lucasdmr24/Funbio-Proyecto/Documentacion/Entregables/Entregable 2/Entregable 2 Corregido.md

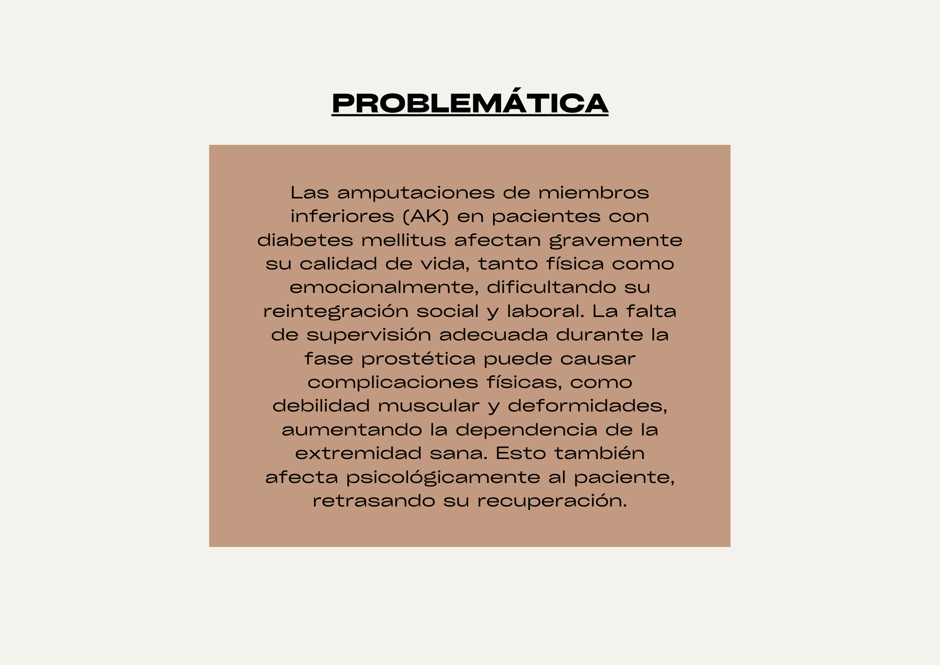
[picture p74: Documentacion/Entregables/Entregable 2/image_0.png]
image alt text
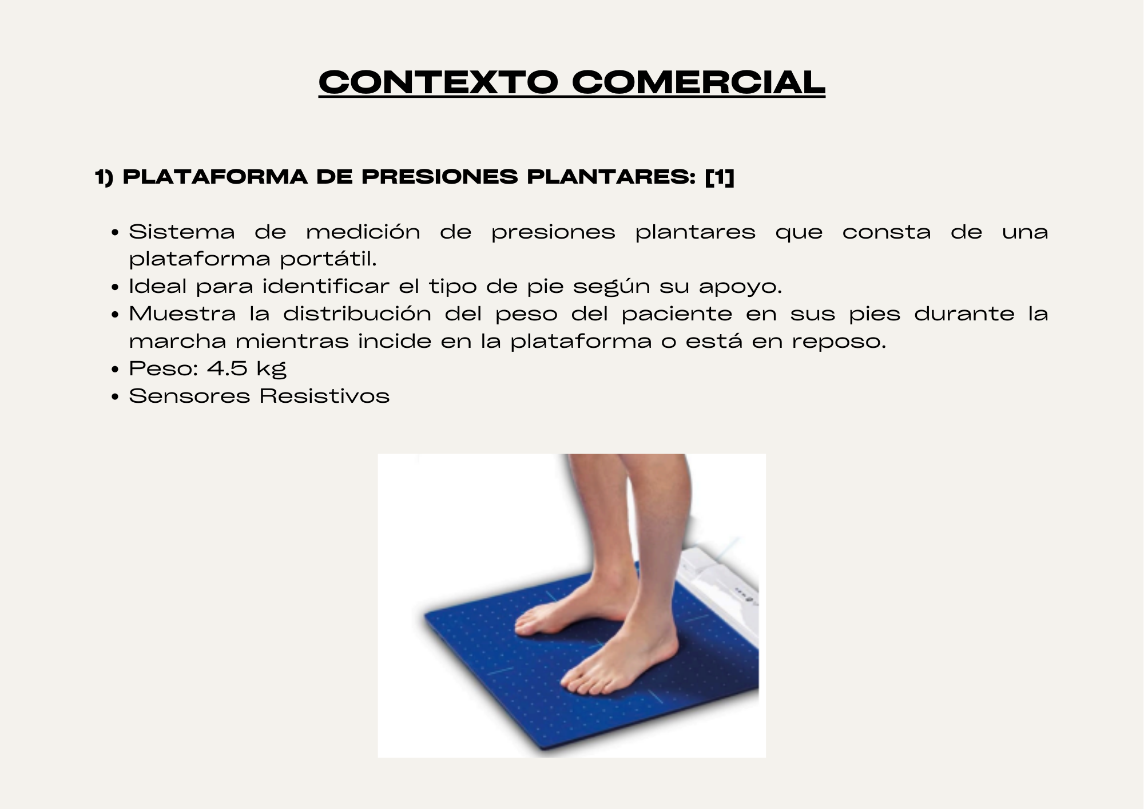
[picture p75: Documentacion/Entregables/Entregable 2/image_1.png]
image alt text
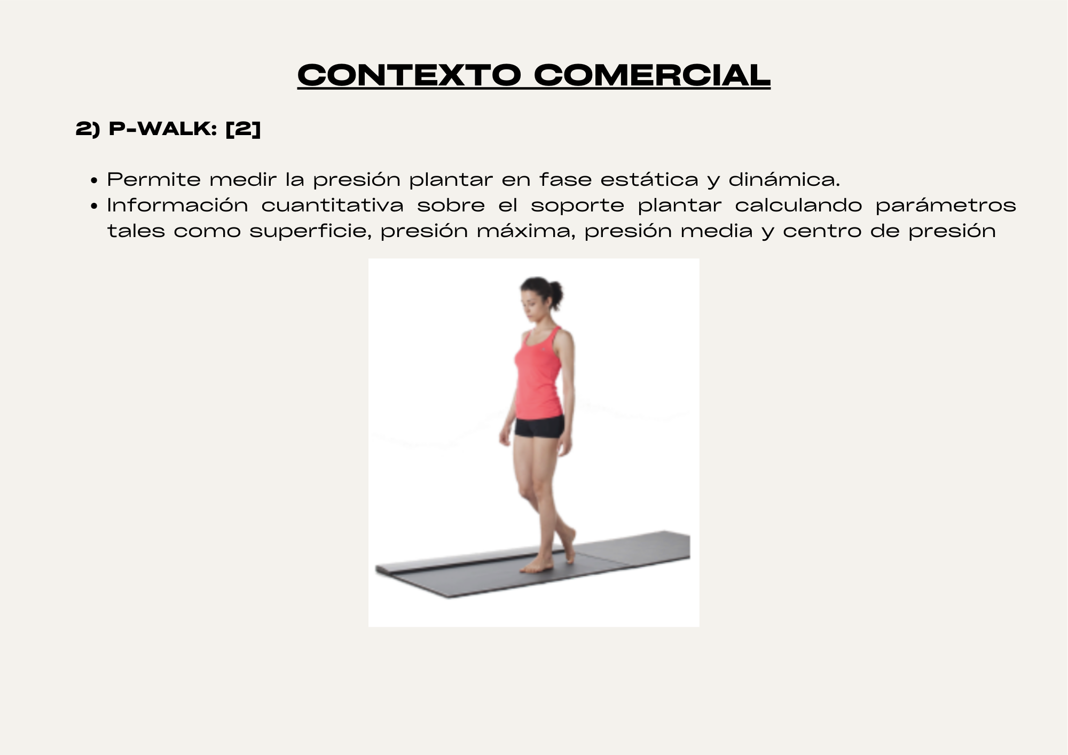
[picture p76: Documentacion/Entregables/Entregable 2/image_2.png]
image alt text
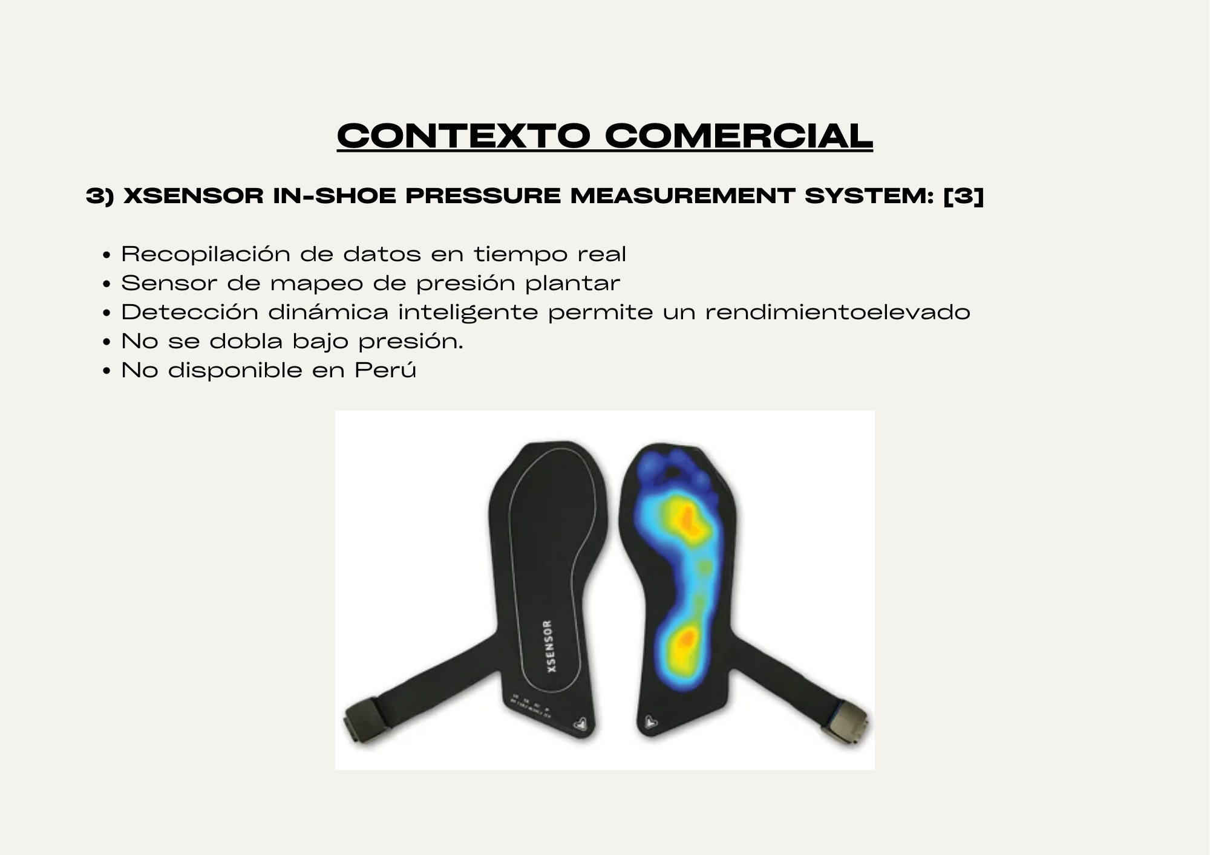
[picture p77: Documentacion/Entregables/Entregable 2/image_3.png]
image alt text
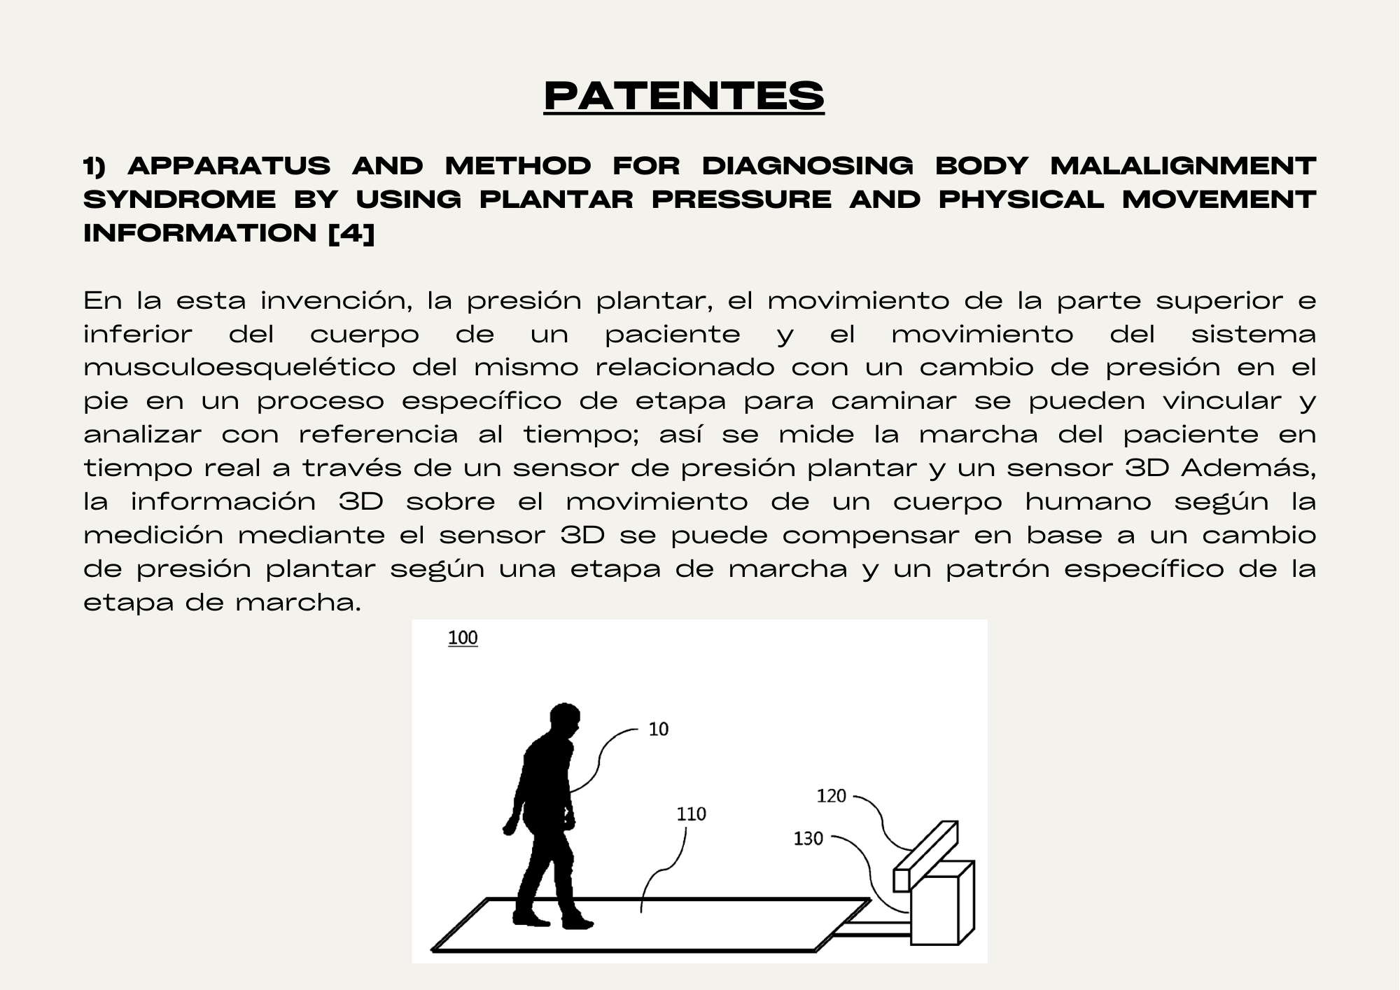
[picture p78: Documentacion/Entregables/Entregable 2/image_4.png]
image alt text
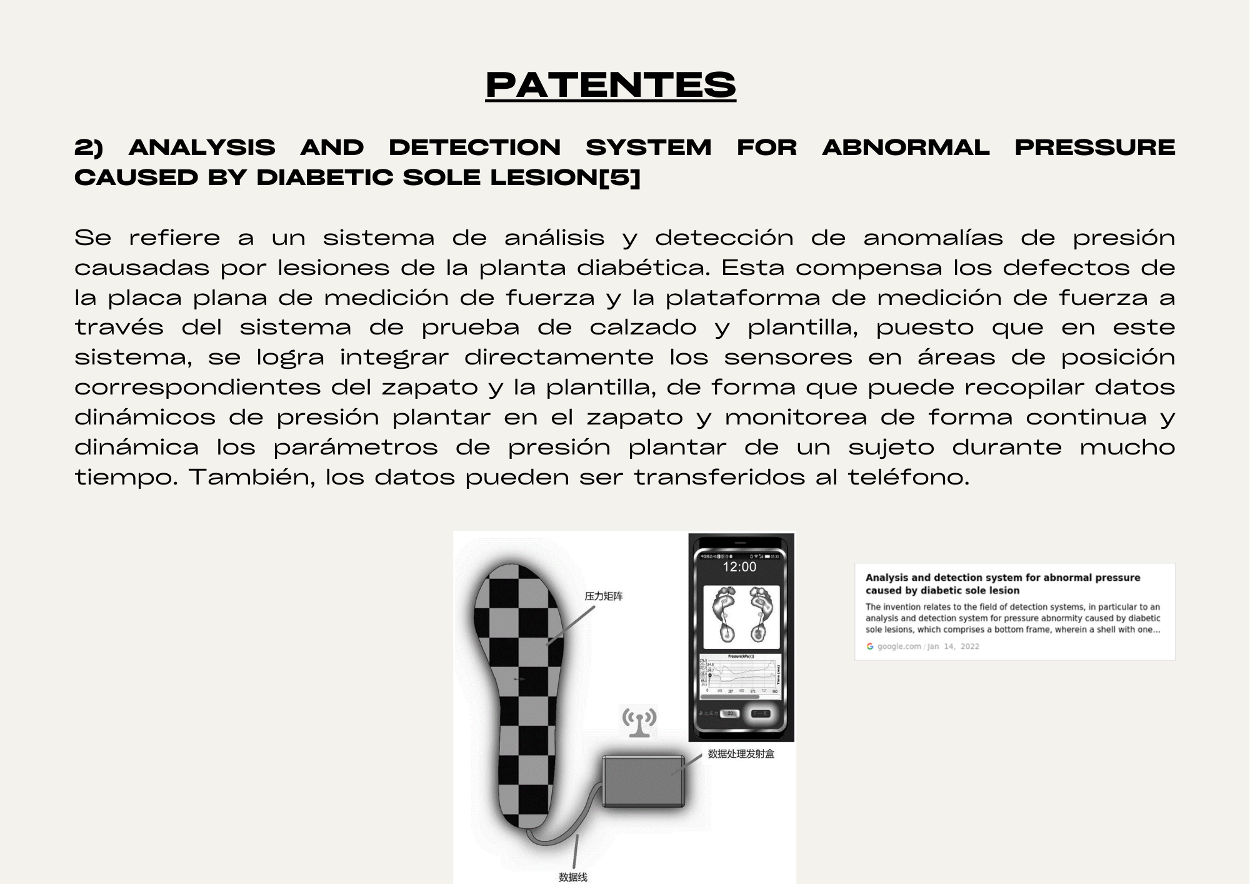
[picture p79: Documentacion/Entregables/Entregable 2/image_5.png]
image alt text
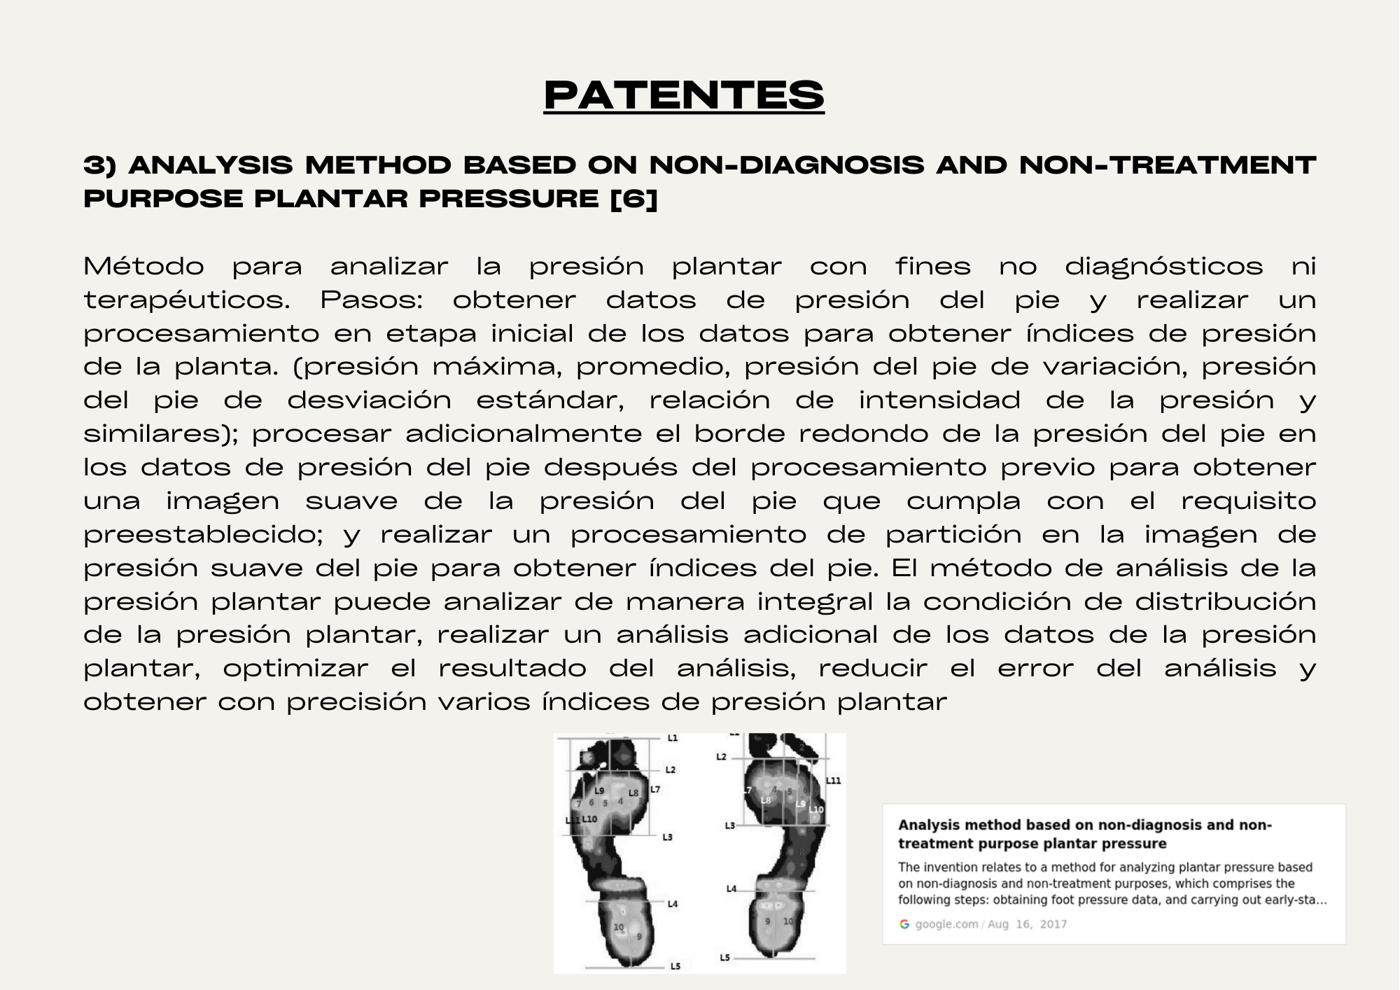
[picture p80: Documentacion/Entregables/Entregable 2/image_6.png]
image alt text
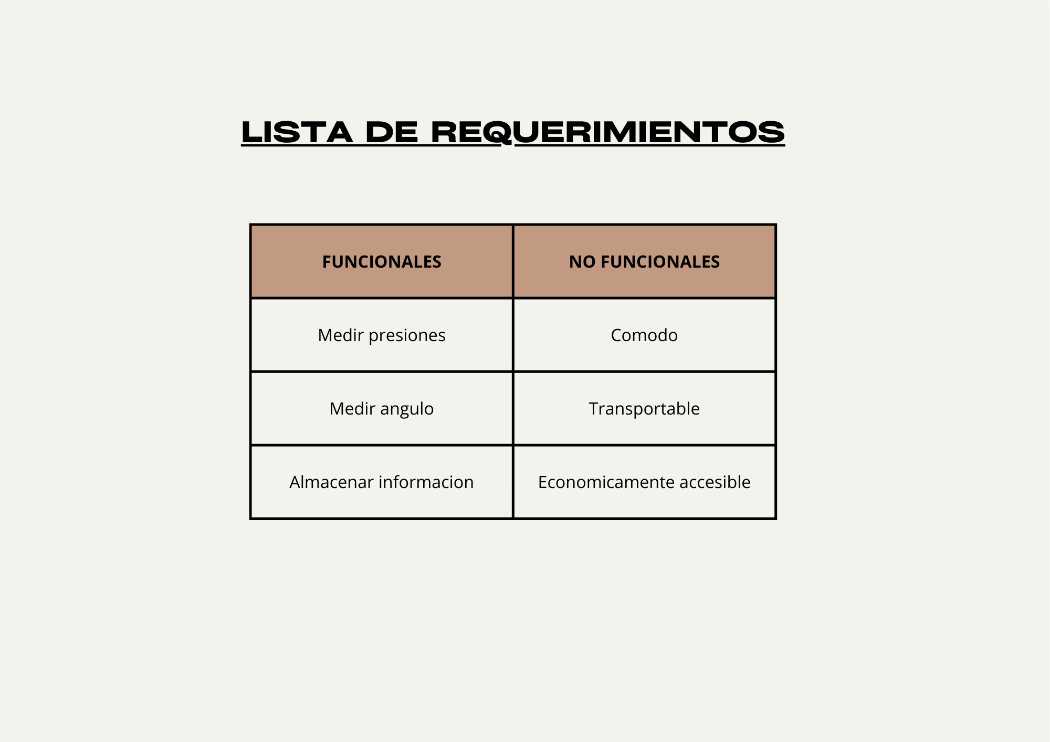
[picture p81: Documentacion/Entregables/Entregable 2/image_7.png]
image alt text
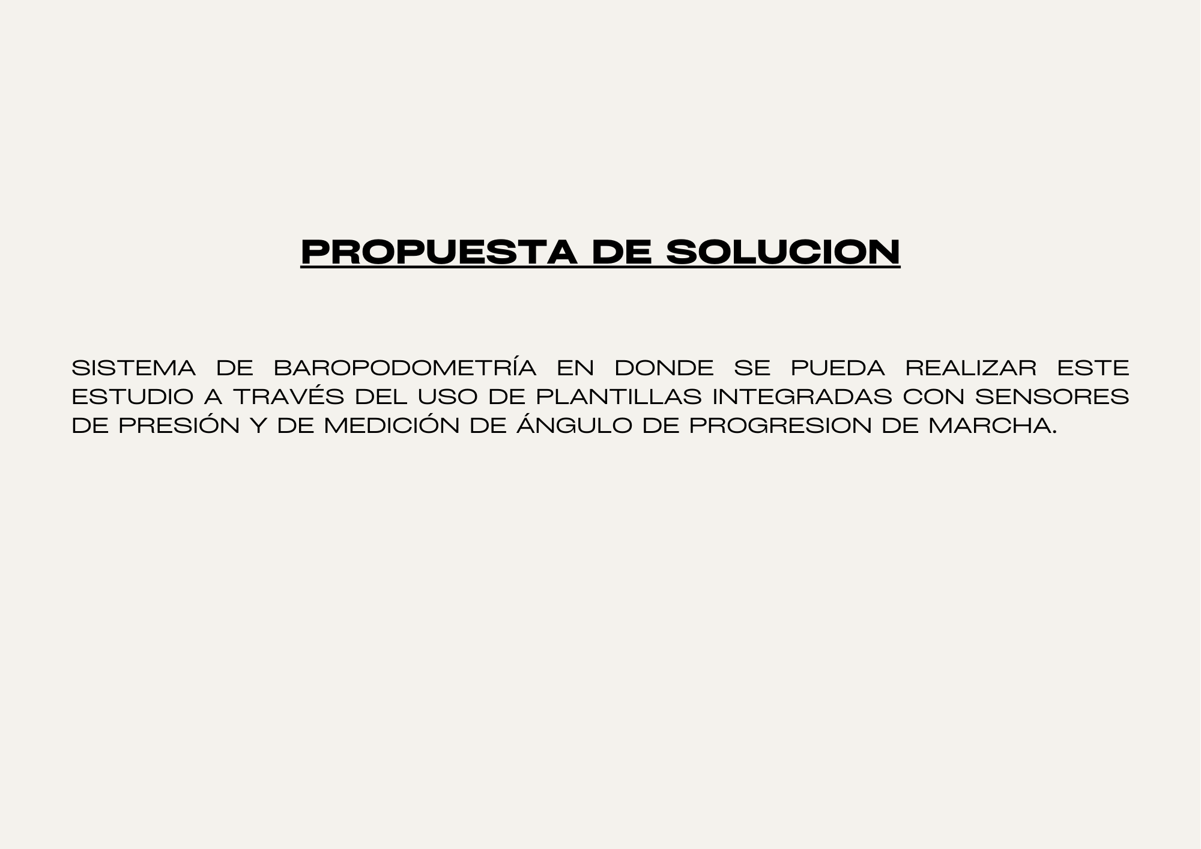
[picture p82: Documentacion/Entregables/Entregable 2/image_8.png]
image alt text
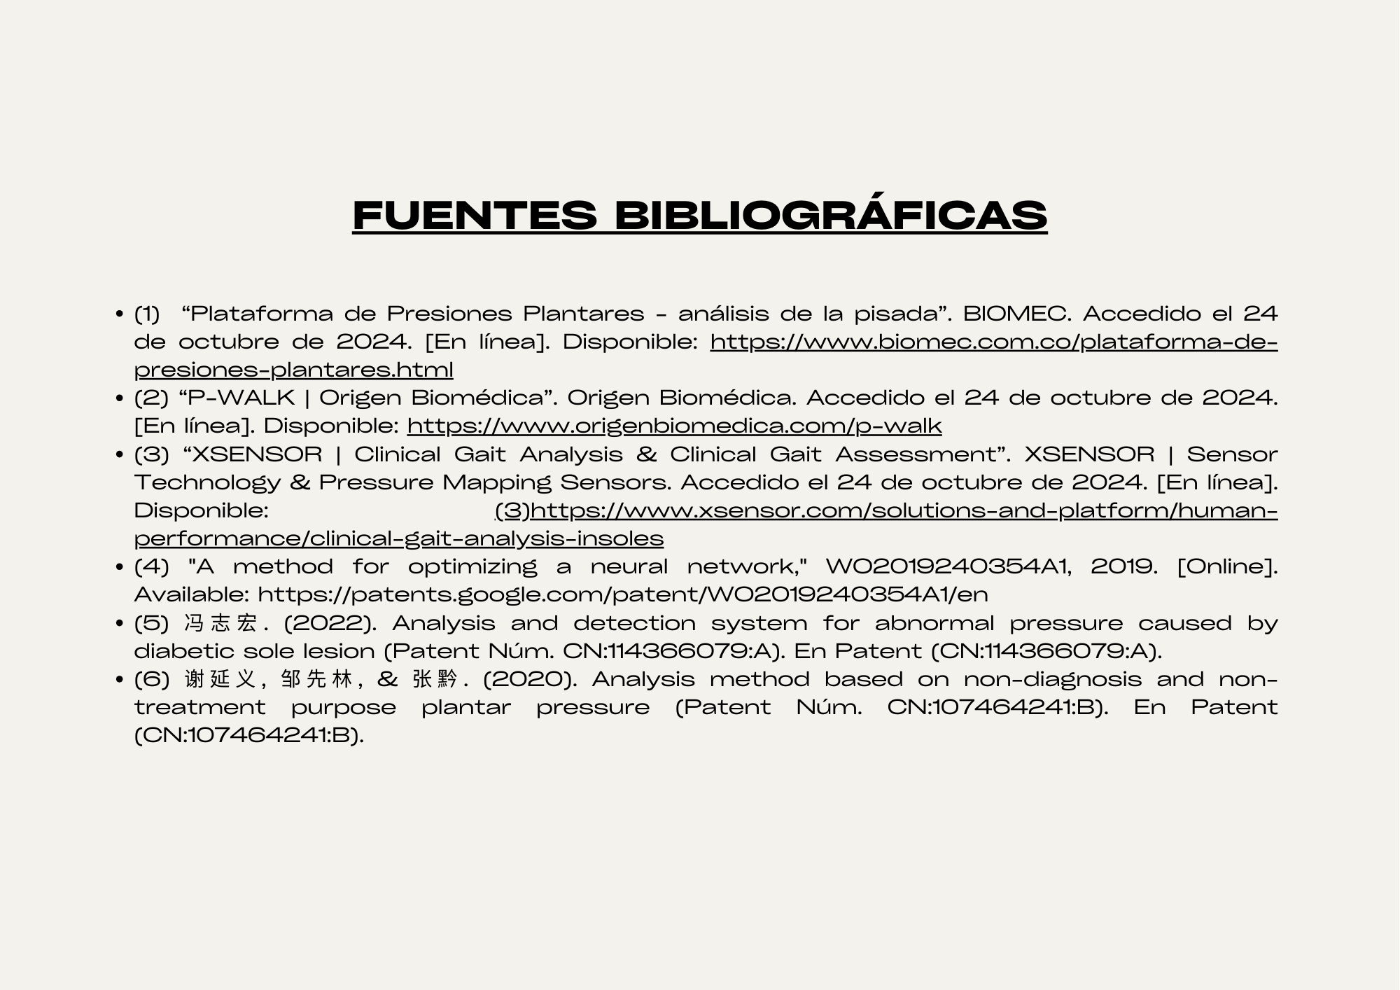
[picture p83: Documentacion/Entregables/Entregable 2/image_9.png]
image alt text
