lucasdmr24/Funbio-Proyecto/Imagenes/Entregable 1/image_0.png

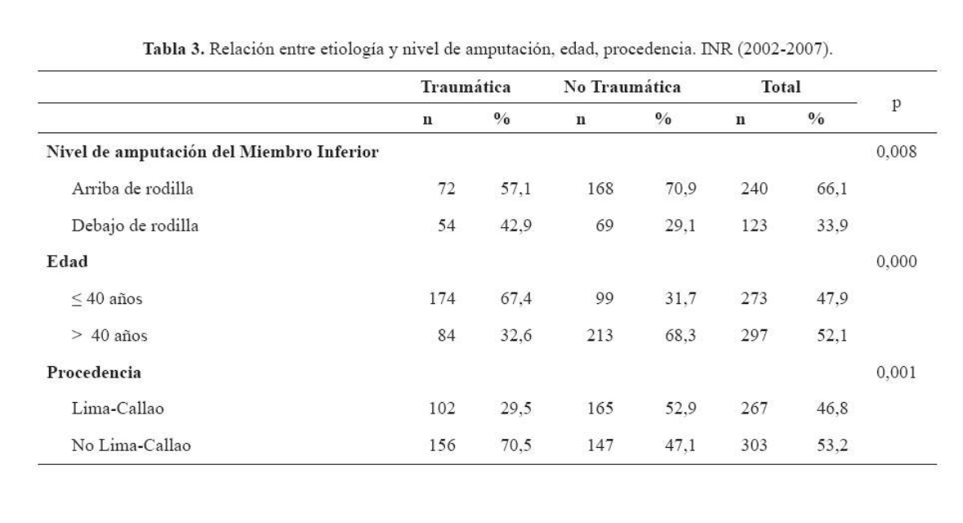
Imagenes/Entregable 1/image_0.png
