lucasdmr24/Funbio-Proyecto/Imagenes/Entregable 1/image_1.jpg

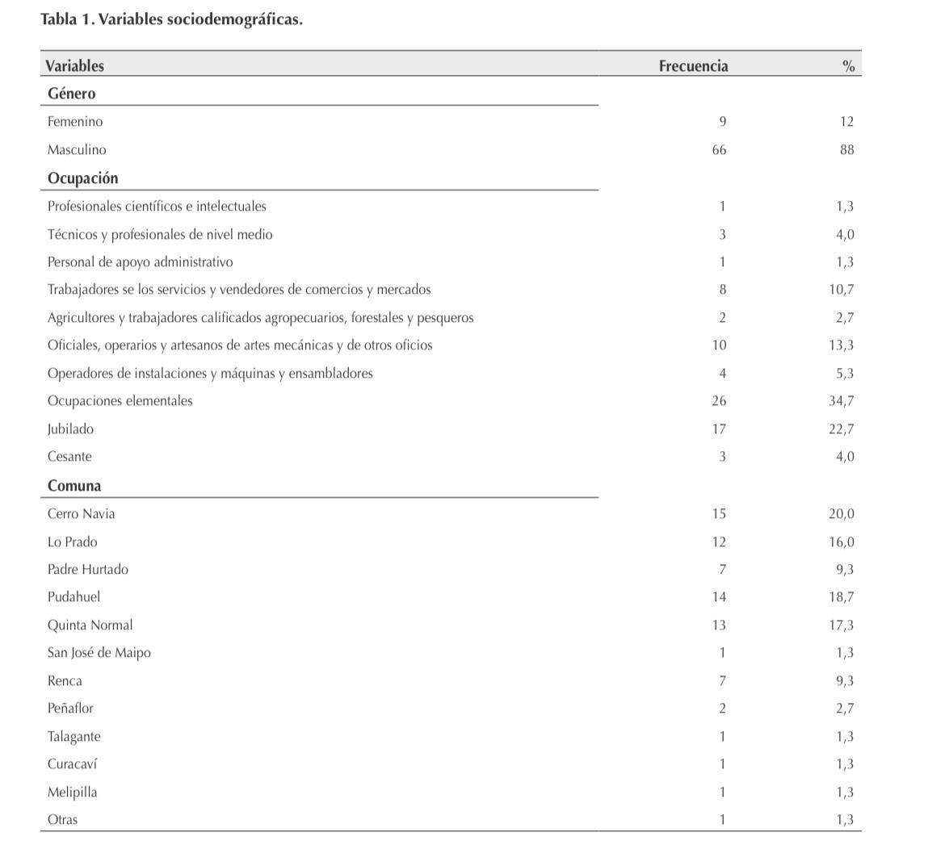
Imagenes/Entregable 1/image_1.jpg
