lucasdmr24/Funbio-Proyecto/Imagenes/Entregable 1/image_2.jpg

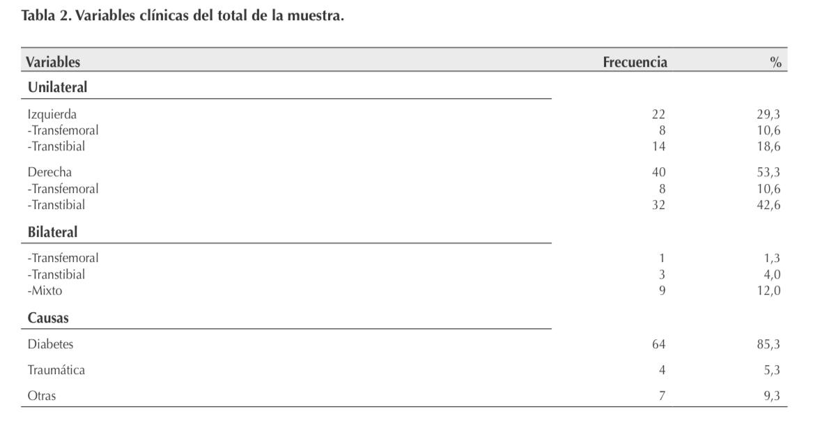
Imagenes/Entregable 1/image_2.jpg
