lucasdmr24/Funbio-Proyecto/Imagenes/Entregable 1/image_3.jpg

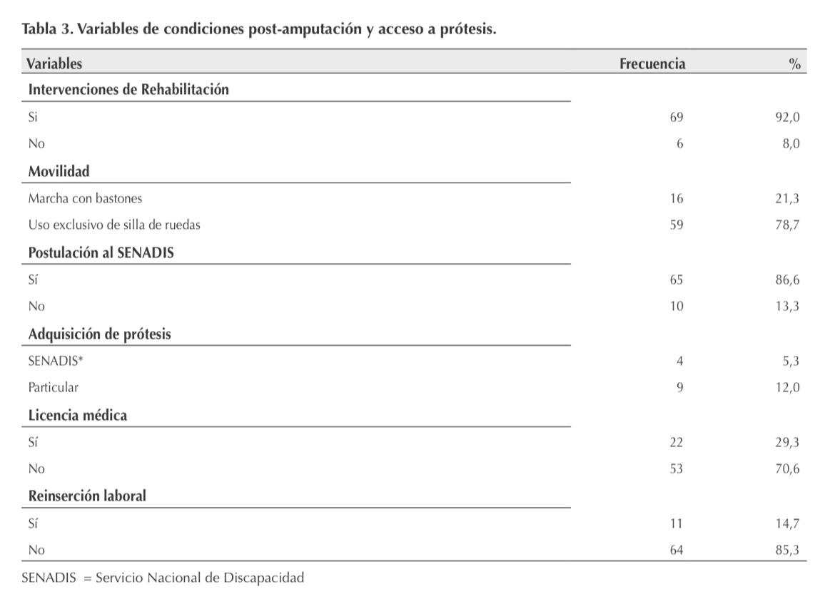
Imagenes/Entregable 1/image_3.jpg
