lucasdmr24/Funbio-Proyecto/Imagenes/Entregable 1/image_4.jpg

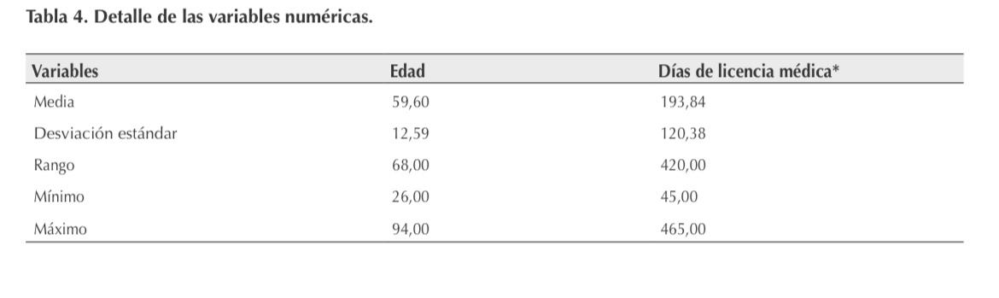
Imagenes/Entregable 1/image_4.jpg
