lucasdmr24/Funbio-Proyecto/Imagenes/Entregable 1/image_5.jpg

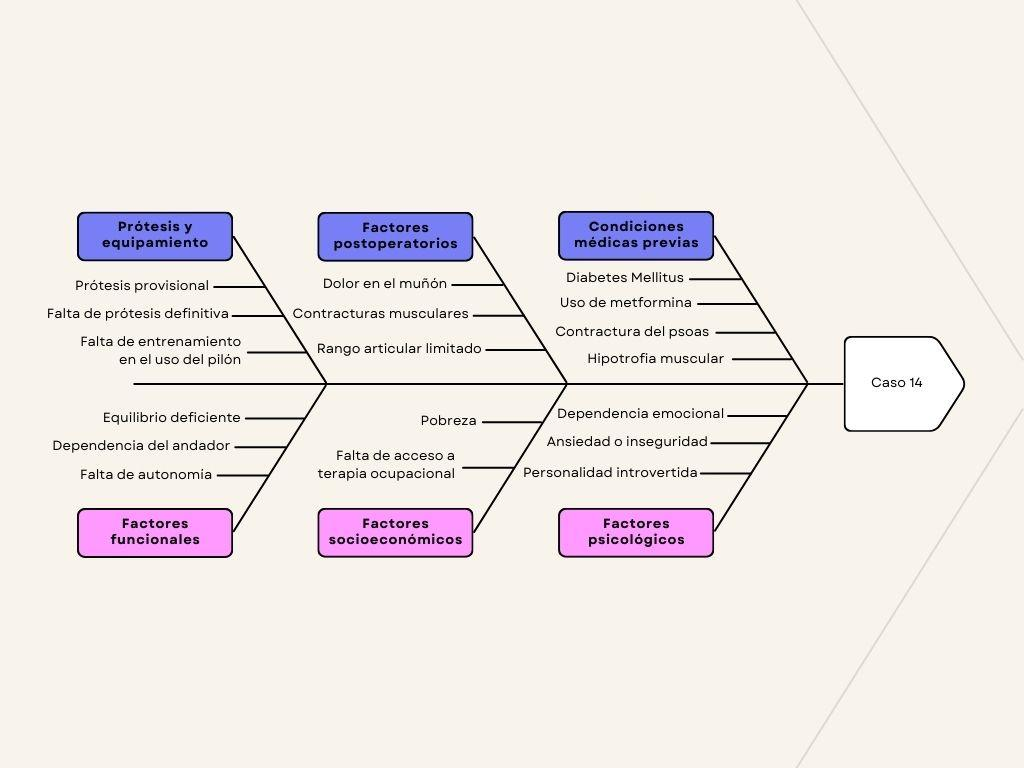
Imagenes/Entregable 1/image_5.jpg
