lucasdmr24/Funbio-Proyecto/Imagenes/Entregable 1/image_6.png

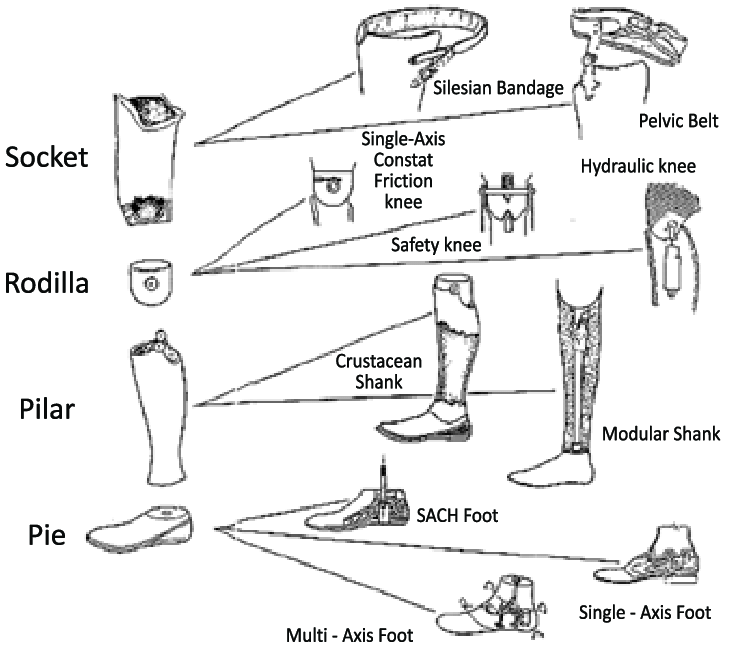
Imagenes/Entregable 1/image_6.png
