lucasdmr24/Funbio-Proyecto/Imagenes/Entregable 1/image_7.png

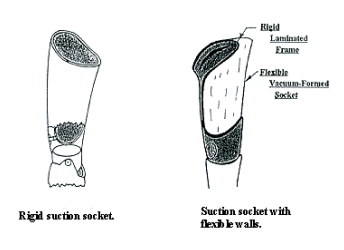
Imagenes/Entregable 1/image_7.png
