lucasdmr24/Funbio-Proyecto/Imagenes/Entregable 1/image_8.png

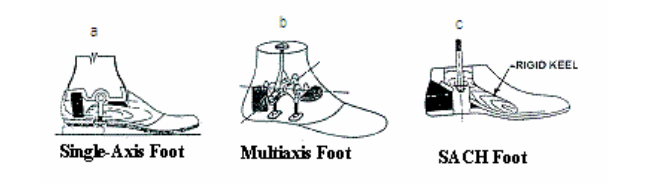
Imagenes/Entregable 1/image_8.png
