lucasdmr24/Funbio-Proyecto/Imagenes/Entregable 1/image_9.png

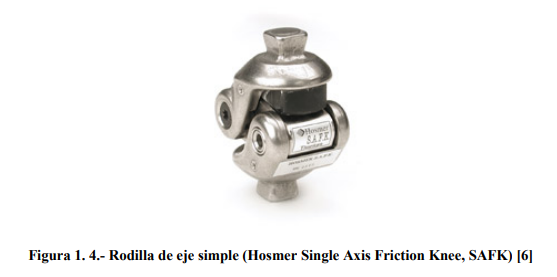
Imagenes/Entregable 1/image_9.png
