lucasdmr24/Funbio-Proyecto/Imagenes/Entregable 1/image_10.png

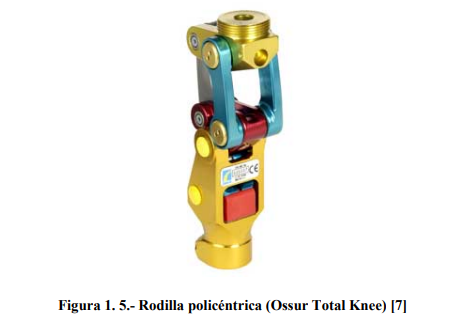
Imagenes/Entregable 1/image_10.png
