lucasdmr24/Funbio-Proyecto/Imagenes/Entregable 1/image_11.png

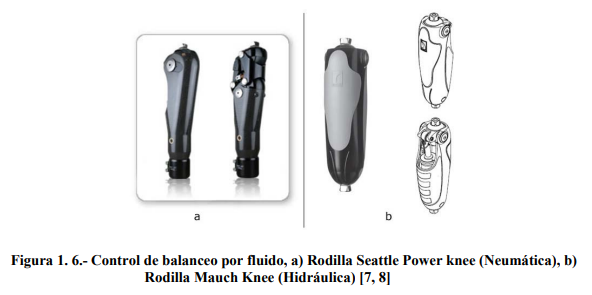
Imagenes/Entregable 1/image_11.png
