lucasdmr24/Funbio-Proyecto/Imagenes/Entregable 2/image_0.png

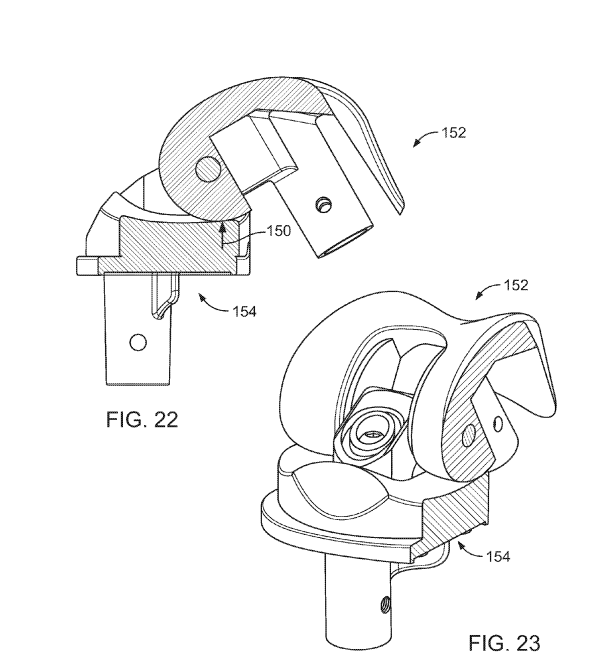
Imagenes/Entregable 2/image_0.png
