lucasdmr24/Funbio-Proyecto/Imagenes/Entregable 2/image_1.png

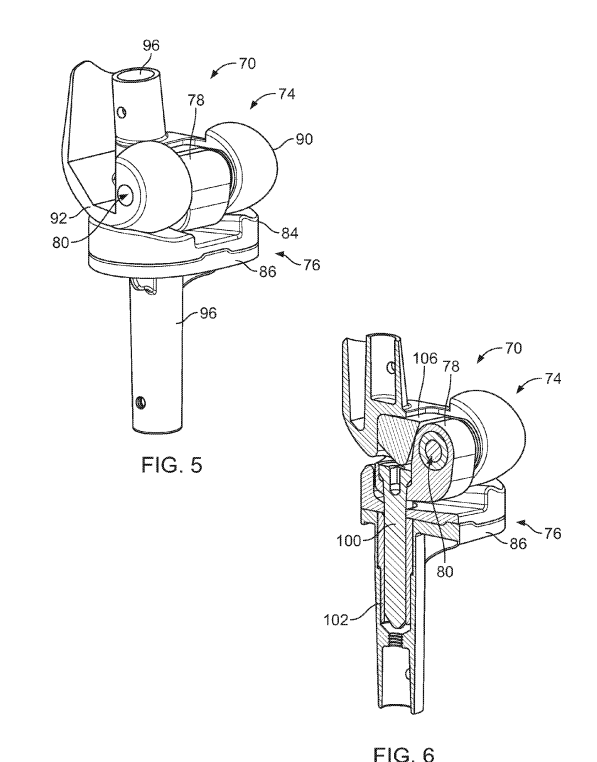
Imagenes/Entregable 2/image_1.png
