lucasdmr24/Funbio-Proyecto/Imagenes/Entregable 2/image_2.jpg

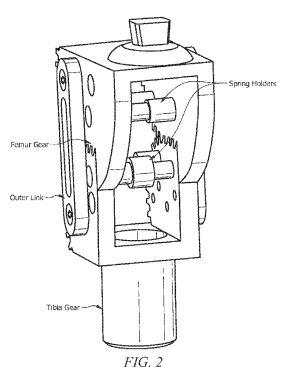
Imagenes/Entregable 2/image_2.jpg
