lucasdmr24/Funbio-Proyecto/Imagenes/Entregable 2/image_3.jpg

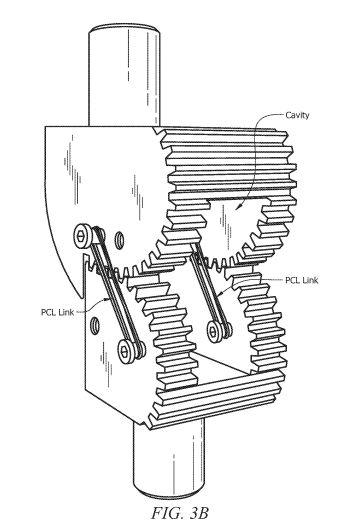
Imagenes/Entregable 2/image_3.jpg
