lucasdmr24/Funbio-Proyecto/Imagenes/Entregable 2/image_4.jpg

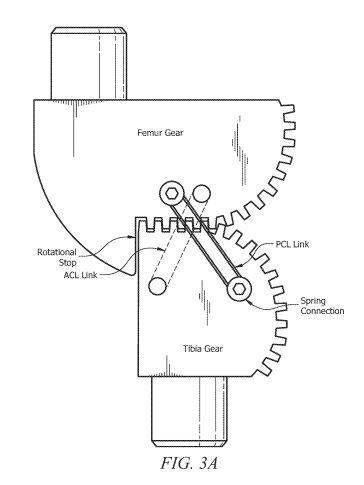
Imagenes/Entregable 2/image_4.jpg
