lucasdmr24/Funbio-Proyecto/Imagenes/Entregable 2/image_5.png

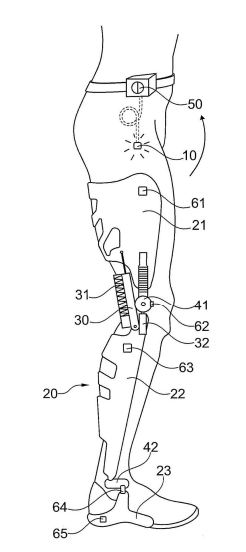
Imagenes/Entregable 2/image_5.png
