lucasdmr24/Funbio-Proyecto/Imagenes/Entregable 2/image_6.png

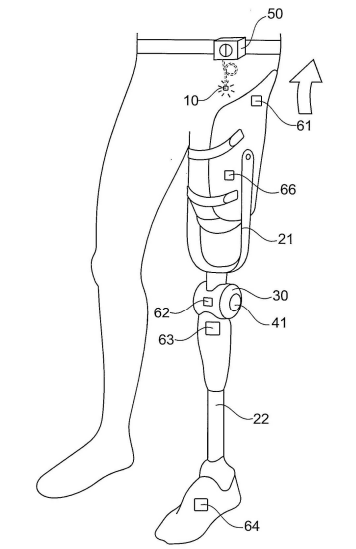
Imagenes/Entregable 2/image_6.png
